ethanjli/fermentor/design/mechanical/impeller/Combined rear.PNG

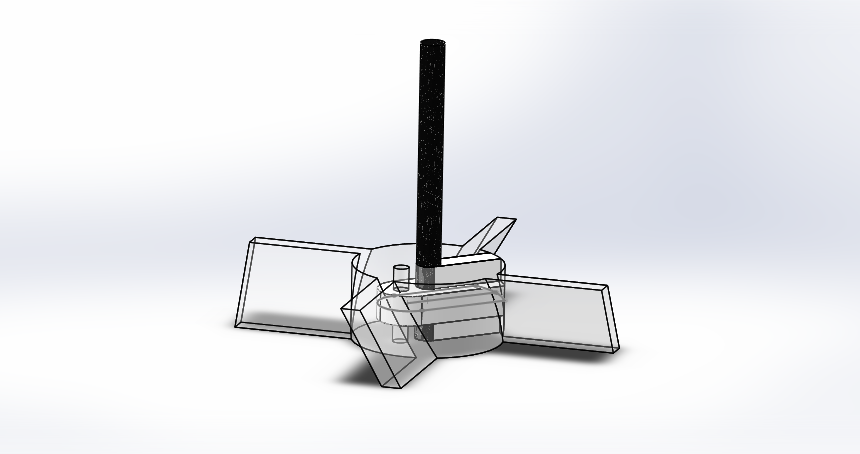
design/mechanical/impeller/Combined rear.PNG
