ethanjli/fermentor/design/mechanical/impeller/Combined.PNG

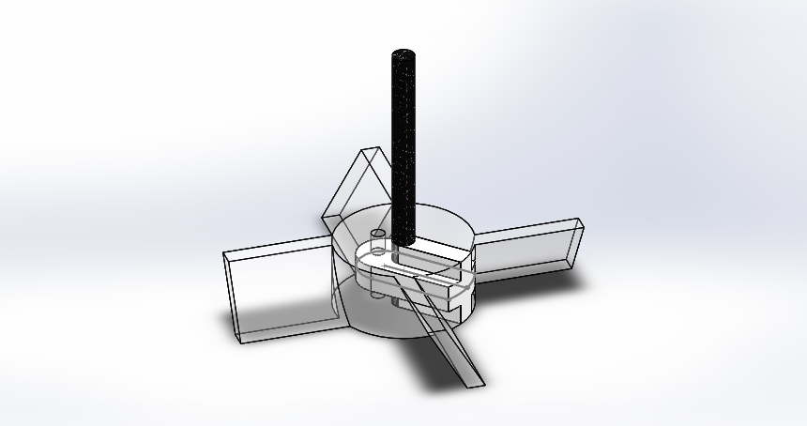
design/mechanical/impeller/Combined.PNG
