ethanjli/fermentor/design/mechanical/impeller/Impeller.PNG

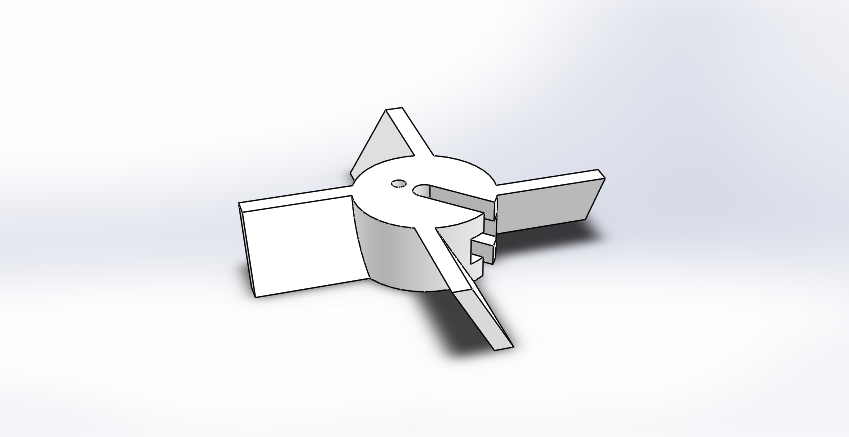
design/mechanical/impeller/Impeller.PNG
