ethanjli/fermentor/design/mechanical/vessel/VesselLEDs.PNG

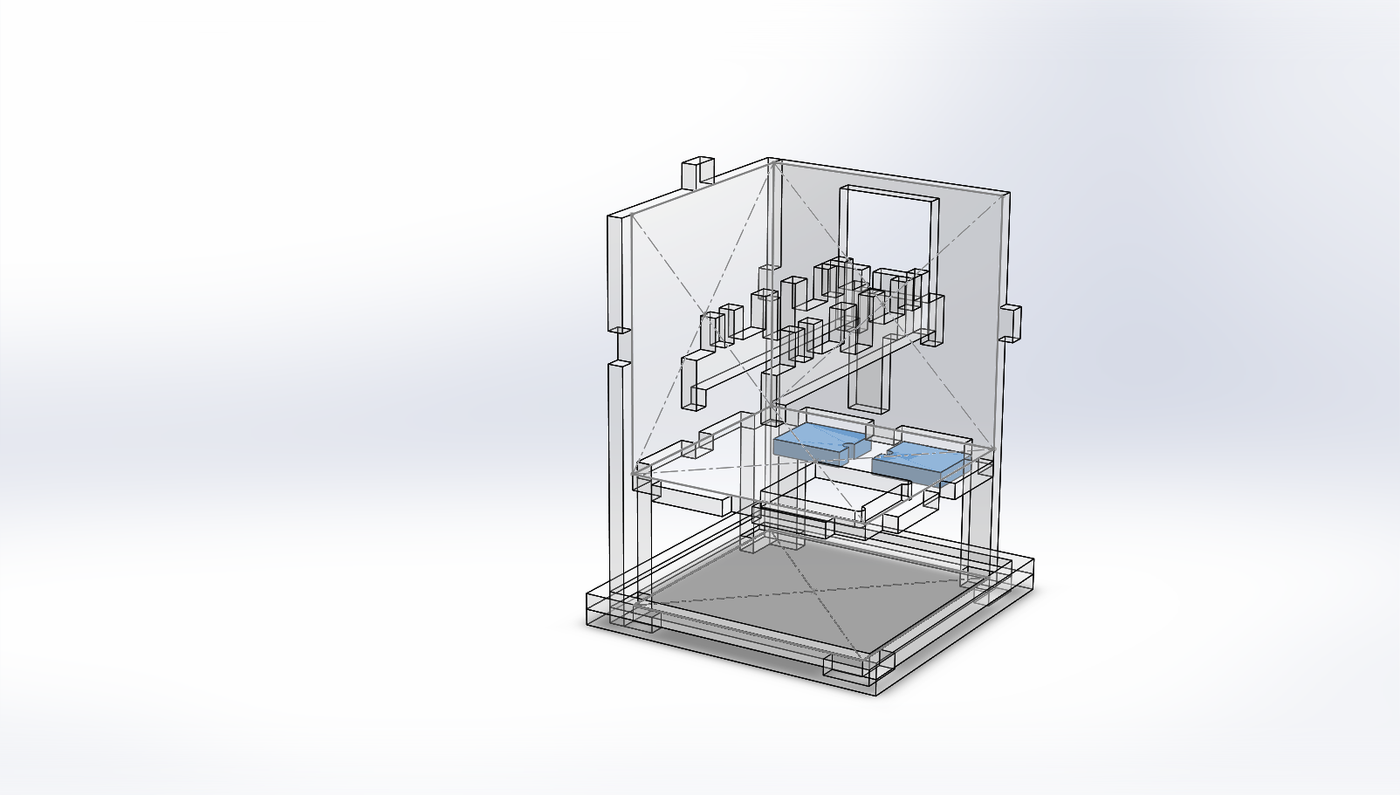
design/mechanical/vessel/VesselLEDs.PNG
