ethanjli/fermentor/design/mechanical/vessel/Motor Alignment Plate.SLDPRT

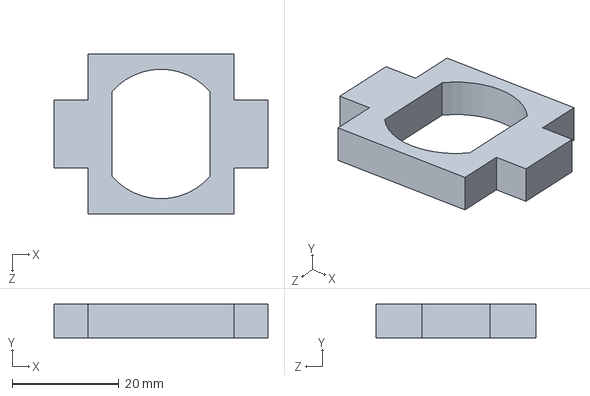
[picture p31: CAD file, 2016-12-07]
design/mechanical/vessel/Motor Alignment Plate.SLDPRT
40.0 x 6.35 x 30.0 mm
