ethanjli/fermentor/design/mechanical/vessel/Lid.SLDPRT

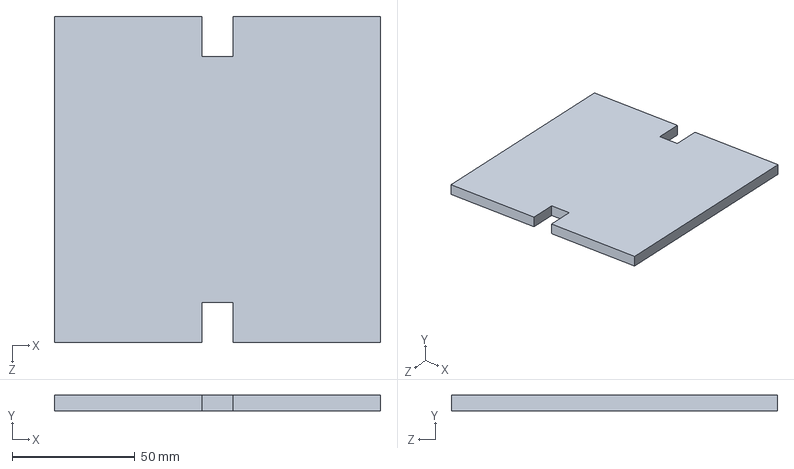
[picture p32: CAD file, 2016-12-07]
design/mechanical/vessel/Lid.SLDPRT
132.7 x 6.35 x 132.7 mm
